jousis9/ESPresso-Scale/Hardware/PCB Images/Lunar Eclipse v4/bottom.jpg

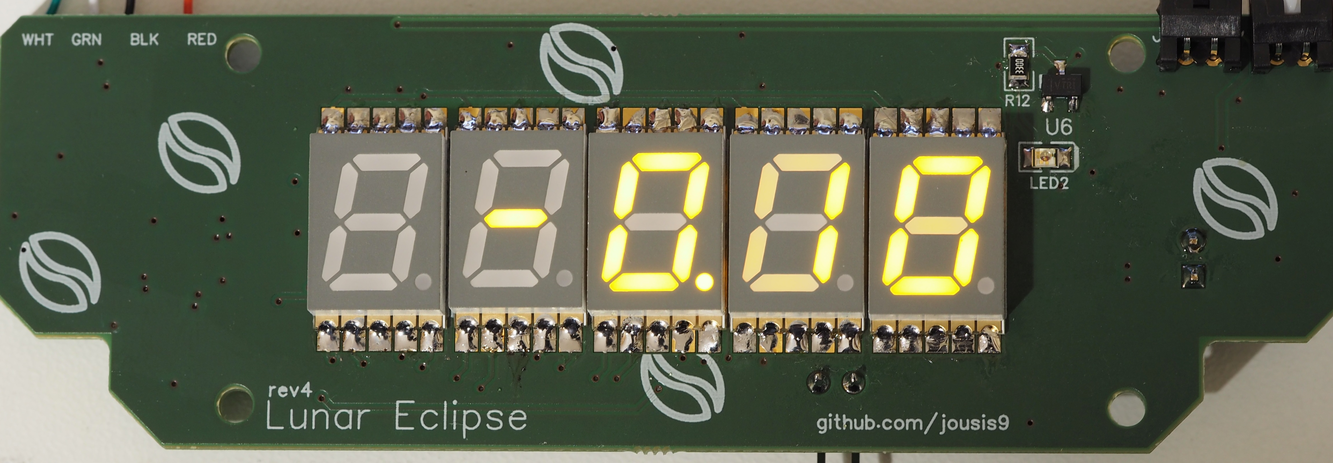
Hardware/PCB Images/Lunar Eclipse v4/bottom.jpg
