jousis9/ESPresso-Scale/Hardware/PCB Images/Lunar Eclipse v4/top.jpg

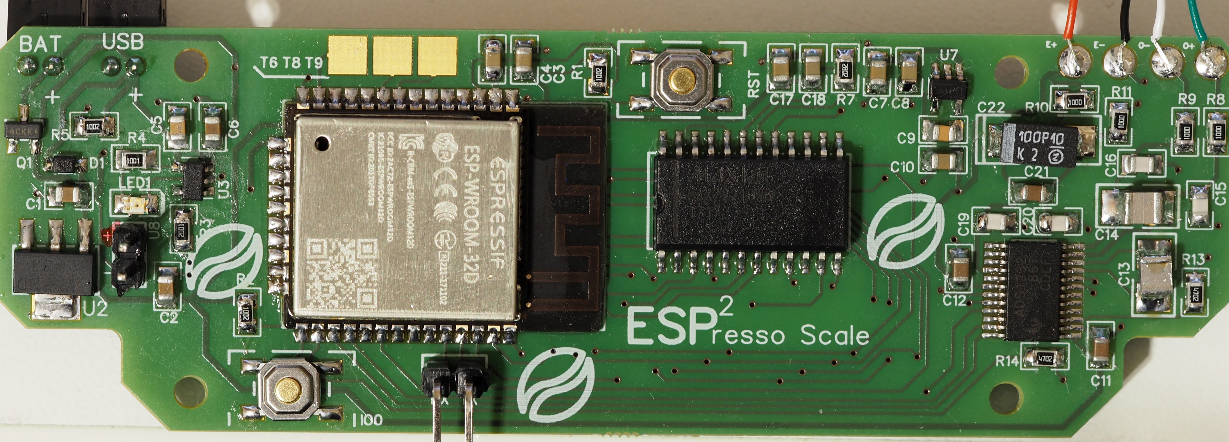
Hardware/PCB Images/Lunar Eclipse v4/top.jpg
