jousis9/ESPresso-Scale/Hardware/PCB Images/PRO v2/bottom01.jpg

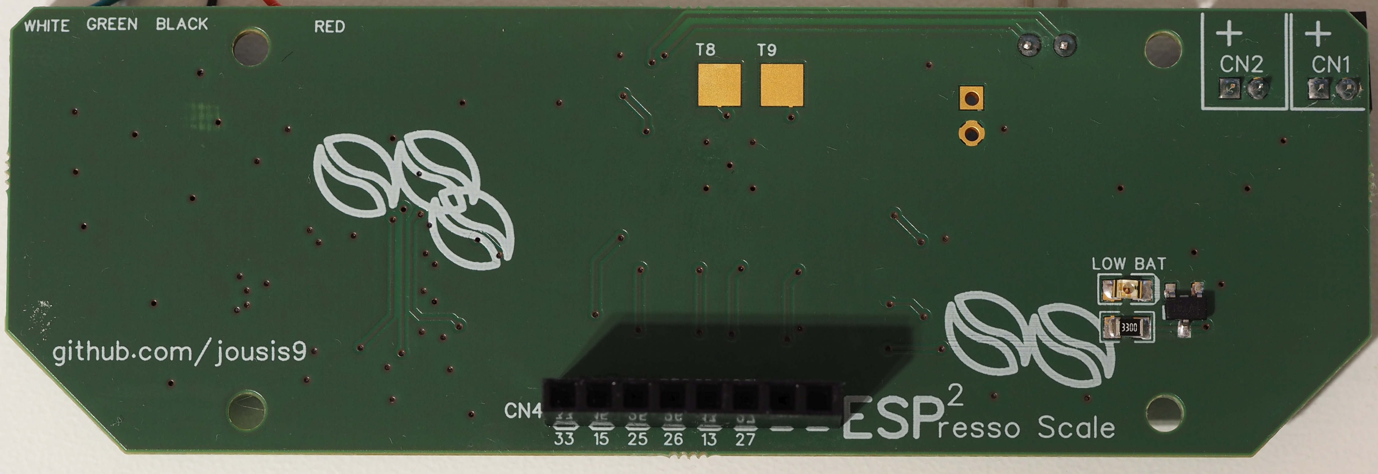
Hardware/PCB Images/PRO v2/bottom01.jpg
