jousis9/ESPresso-Scale/Hardware/PCB Images/PRO v2/top.jpg

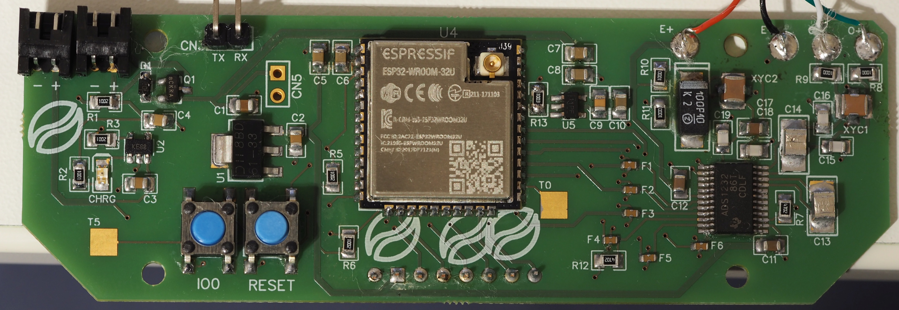
Hardware/PCB Images/PRO v2/top.jpg
