jousis9/ESPresso-Scale/Photos/OTA Upgrade/upgrademode_upgrading2.jpg

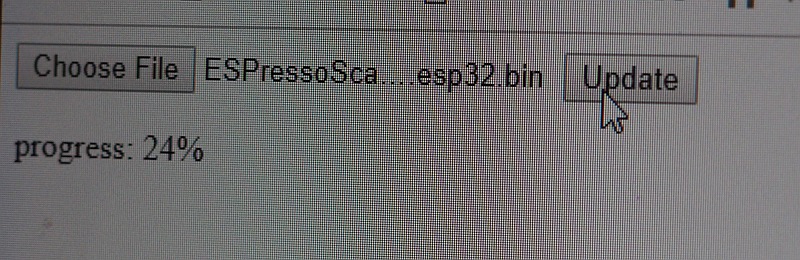
Photos/OTA Upgrade/upgrademode_upgrading2.jpg
