jousis9/ESPresso-Scale/Photos/OTA Upgrade/upgrademode_upgrading.jpg

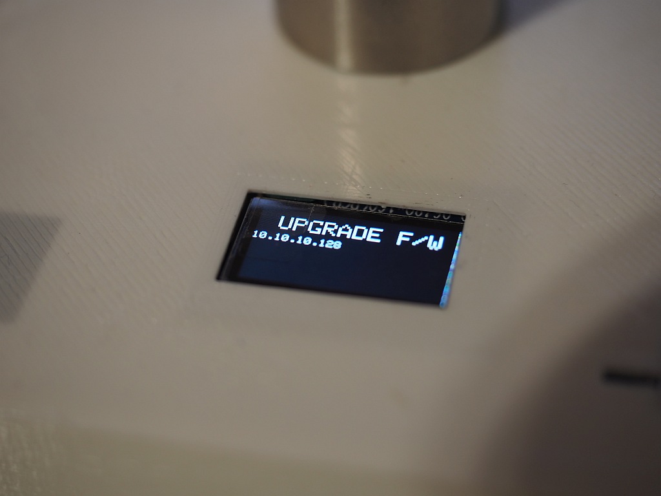
Photos/OTA Upgrade/upgrademode_upgrading.jpg
