jousis9/ESPresso-Scale/Photos/OTA Upgrade/uprademode_fileselection.jpg

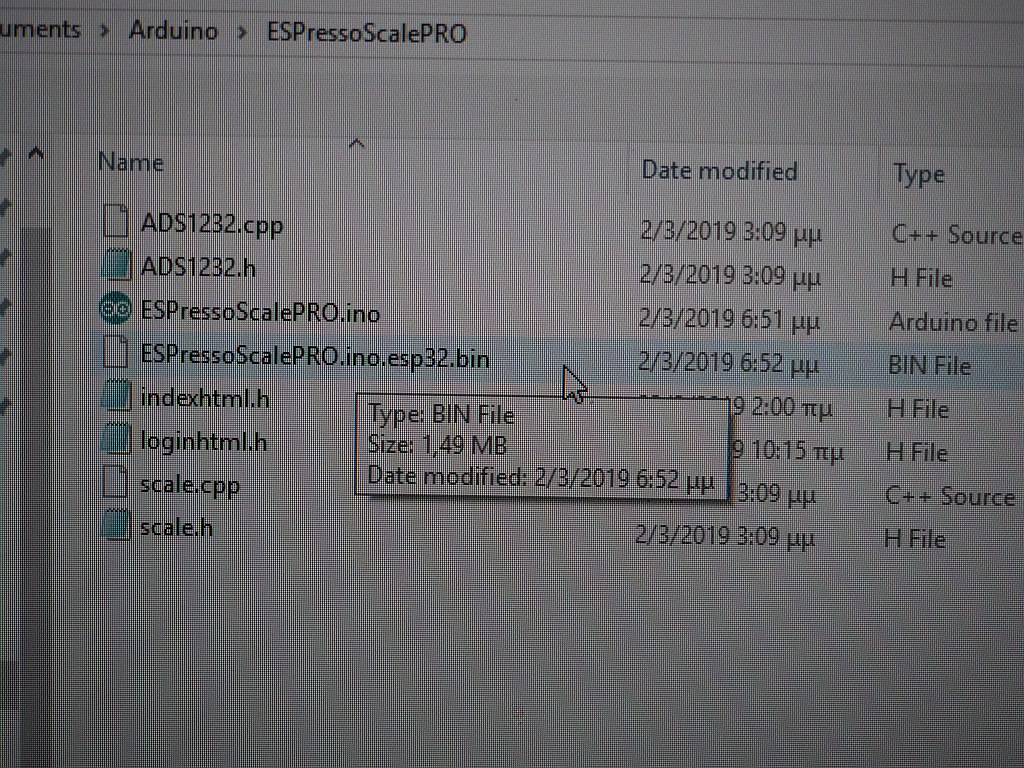
Photos/OTA Upgrade/uprademode_fileselection.jpg
