jousis9/ESPresso-Scale/Photos/OTA Upgrade/uprademode_login.jpg

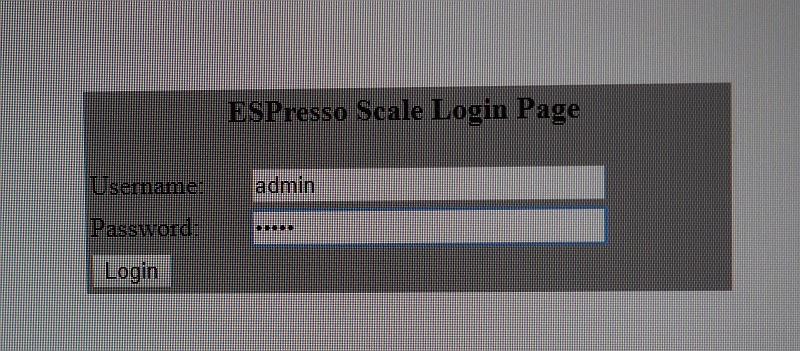
Photos/OTA Upgrade/uprademode_login.jpg
