jousis9/ESPresso-Scale/Photos/OTA Upgrade/uprademode_mobileapp.jpg

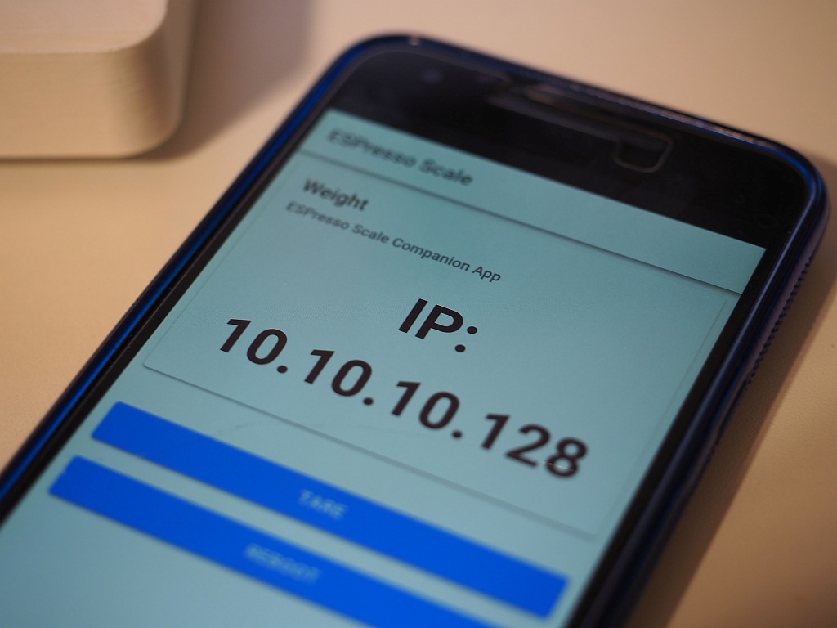
Photos/OTA Upgrade/uprademode_mobileapp.jpg
