jousis9/ESPresso-Scale/Photos/OTA Upgrade/uprademode_readytoupgrade.jpg

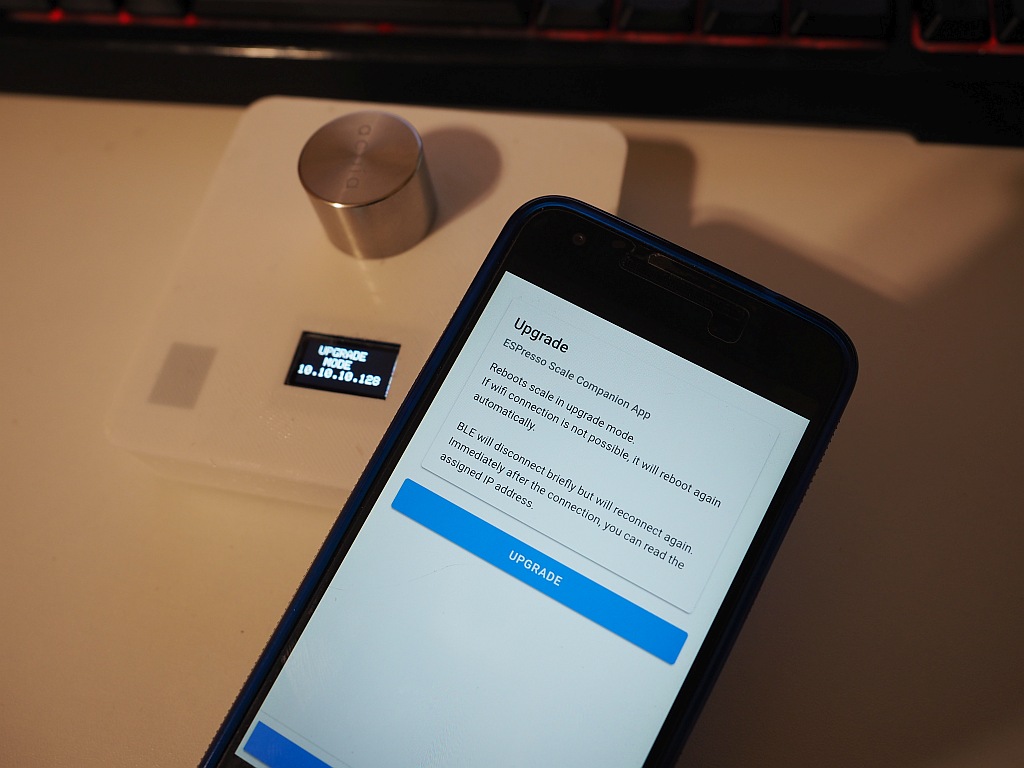
Photos/OTA Upgrade/uprademode_readytoupgrade.jpg
