jousis9/ESPresso-Scale/Photos/Other/booting.jpg

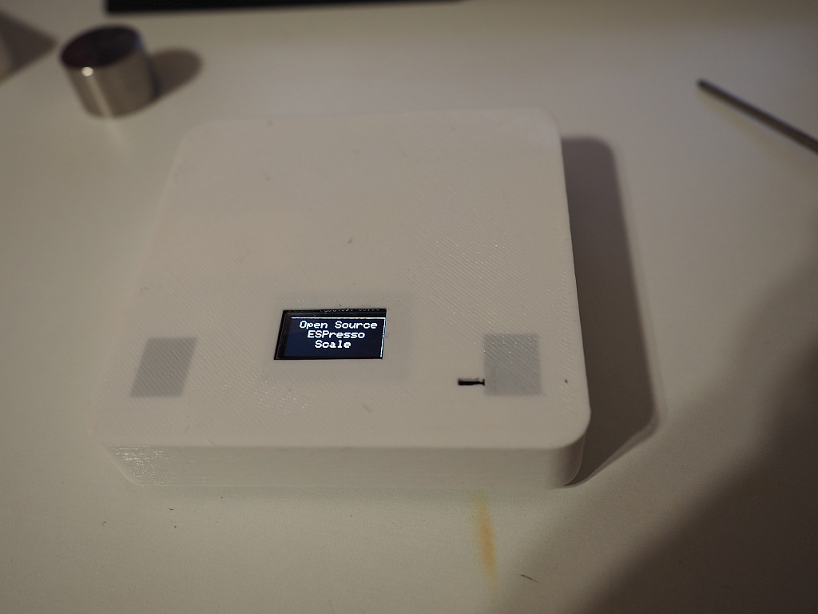
Photos/Other/booting.jpg
