jousis9/ESPresso-Scale/Photos/Other/naked_upside_down.jpg

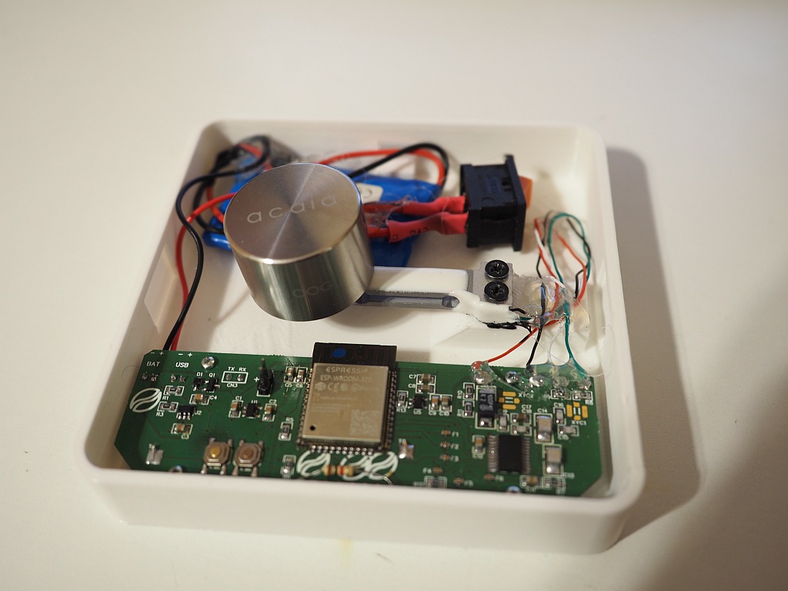
Photos/Other/naked_upside_down.jpg
