jousis9/ESPresso-Scale/Photos/Other/calibration.jpg

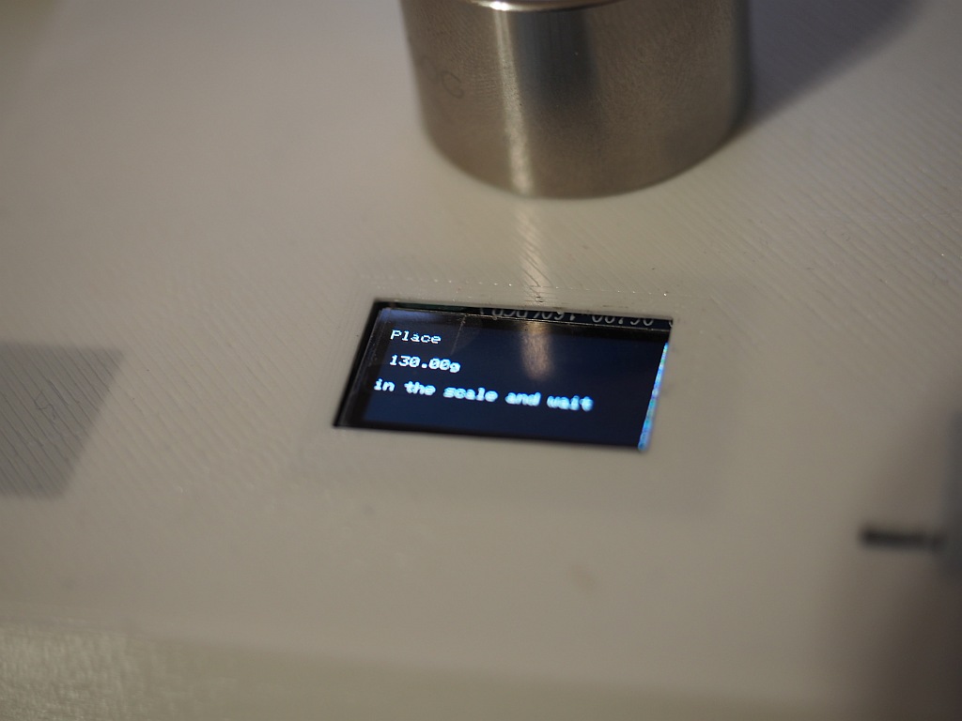
Photos/Other/calibration.jpg
