jousis9/ESPresso-Scale/Photos/Other/calibration_done.jpg

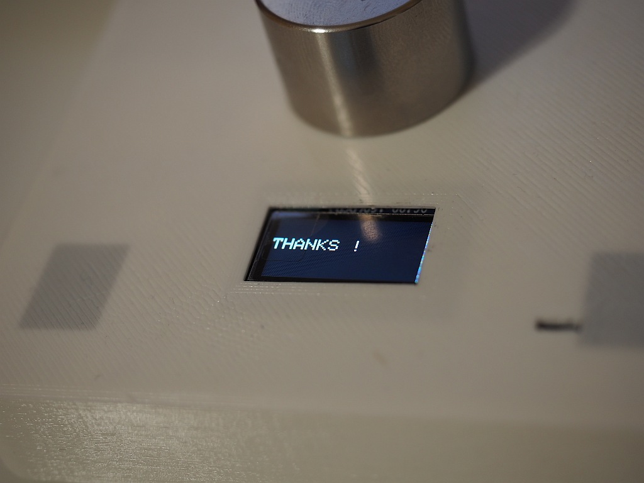
Photos/Other/calibration_done.jpg
