jousis9/ESPresso-Scale/Software/Firmware/ESPressoScalePRO/loginhtml.h

R"rawText(

 <form name="loginForm">
    <table width="20%" bgcolor="A09F9F" align="center">
        <tr>
            <td colspan=2>
                <center><font size=4><b>ESPresso Scale Login Page</b></font></center>
                <br>
            </td>
            <br>
            <br>
        </tr>
        <td>Username:</td>
        <td><input type="text" size=25 name="userid"><br></td>
        </tr>
        <br>
        <br>
        <tr>
            <td>Password:</td>
            <td><input type="Password" size=25 name="pwd"><br></td>
            <br>
            <br>
        </tr>
        <tr>
            <td><input type="submit" onclick="check(this.form)" value="Login"></td>
        </tr>
    </table>
</form>
<script>
    function check(form)
    {
    if(form.userid.value=="admin" && form.pwd.value=="admin")
    {
    window.open("/main")
    }
    else
    {
     alert("Error Password or Username")/*displays error message*/
    }
    }
</script>

)rawText"
